mariaghitaa/InkTime/Images/pcb_3D_bottom.png

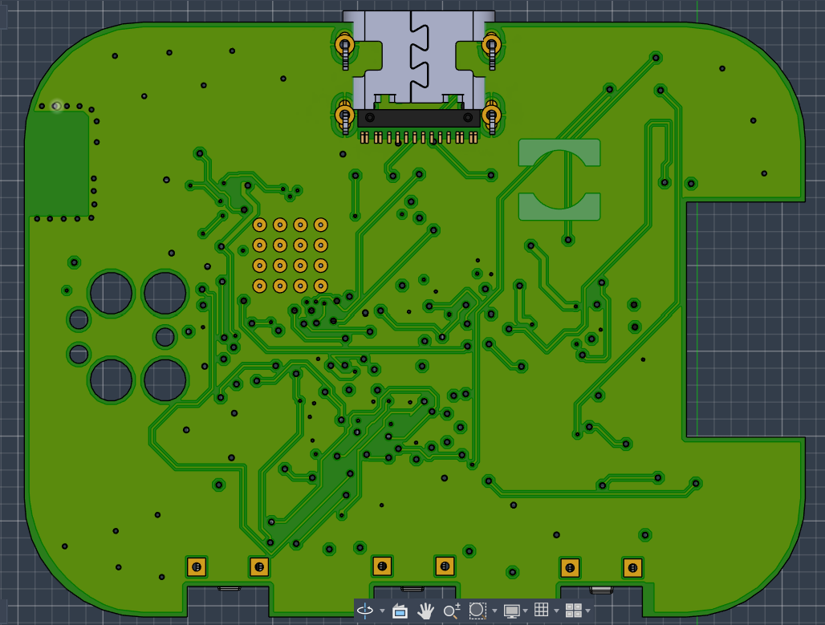
Images/pcb_3D_bottom.png
