mariaghitaa/InkTime/Images/InkTime_assembly.png

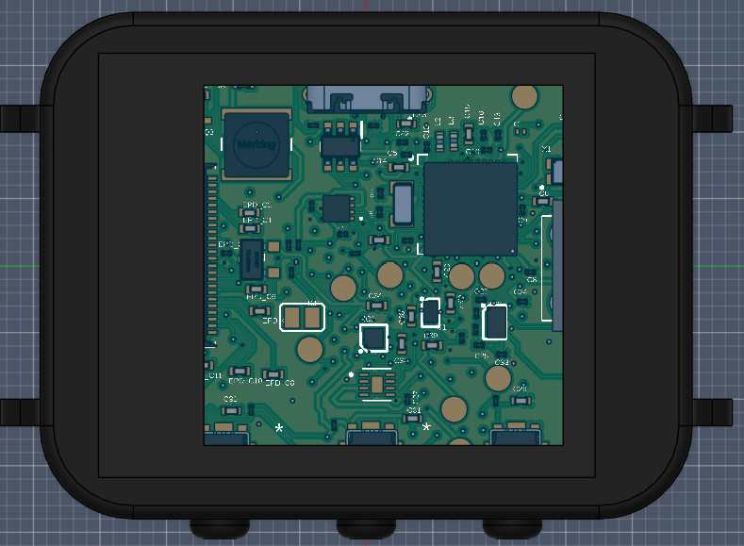
Images/InkTime_assembly.png
